liakhovitch/cronch/pcb/effectpedal/footprints/SJ2-3574A-SMT-TR.stp

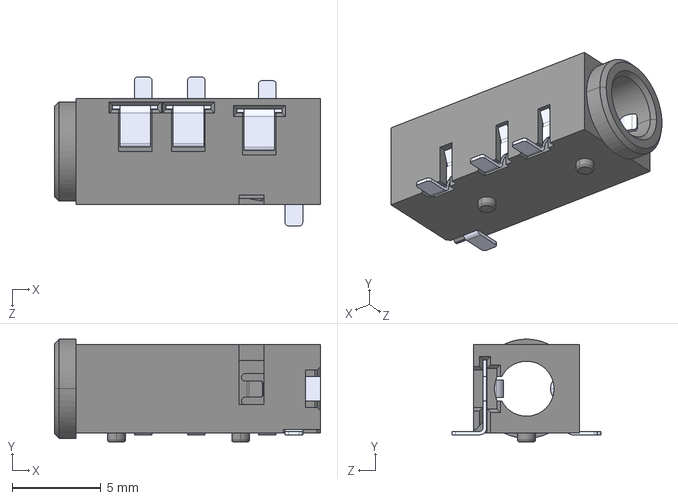
[picture p21: CAD file, 2023-01-28]
pcb/effectpedal/footprints/SJ2-3574A-SMT-TR.stp
15.0 x 5.80 x 8.40 mm
